LMWB/Quattro-Stagioni/Simulations/LTSpice/pt1000_messwandler_single_oamp.asc

R1: res; 10k
R2: res; 963
R3: res; 21.1k
R4: res; 22k
R5: res; 0
R6: res; 0
R7: res; 12k
R8: res; 1k
R100: res; 0
R200: res; 0
R_PT_L1: res; 0.5
R_PT_L2: res; 0.5
R_PT_L3: res; 0.5
R_PT_L4: res; 0.5
RL1: res; 12k
RL: res; 10k
RPT1: res; {PT}
RPT: res; {PT}
U1: LT1001
U2: LT1001
V1: voltage; 5
V2: voltage; 1
V3: voltage; 5
Named nets: 0, Vcc, Vee, Diff_Out1, X2, X1, V2, V1, X3, Vref, Diff_Out2, X13, X11, X12
4 Leiter Model PT1000 Sensor
R_PT_Ln = R-Zuleitungen
1500 Ohm = 125 GradC
  750 Ohm = -50 GradC
.step param PT list 996.1 992.2 988.3 984.4 980.4 976.5 972.6 968.7 964.8  1000 1003.9 1007.8 1011.7 1015.6 1019.5 1023.4 1027.3 1031.2 1035.1 1039.0 1042.9 1046.8 1050.7 1054.6 1058.5 1062.4 1066.3 1070.2 1074.0 1077.9 1081.8 1085.7 1089.6 1093.5 1097.3 1101.2 1105.1 1109.0 1112.9 1116.7 1120.6 1124.5 1128.3 1132.2 1136.1 1140.0 1143.8 1147.7 1151.5 1155.4 1159.3 1163.1 1167.0 1170.8 1174.7 1178.6 1182.4 1186.3 1190.1 1194.0 1197.8 1201.7 1205.5 1209.4 1213.2 1217.1 1220.9 1224.7 1228.6 1232.4 1236.3 1240.1 1243.9 1247.8 1251.6 1255.4 1259.3 1263.1 1266.9 1270.8 1274.6 1278.4 1282.2 1286.1 1289.9 1293.7 1297.5 1301.3 1305.2
.op
Auslegung f. 
Verstaerkung = 25
Pt1000
0V Output bei 0 Grad
3V Output bei 70 Grad
Uref = 5V
OP mono supply
Berechnung
E12-Reihe
4 Leiter Model PT1000 Sensor
R_PT_Ln = R-Zuleitungen
1500 Ohm = 125 GradC
  750 Ohm = -50 GradC
.step param PT 920 1400 10
-20 ... 80 Grad map to 0 ... 3V3
